zgtk-guri/Smart-Door-Keeper/3DPrint/STL/HandleVertical2.STL

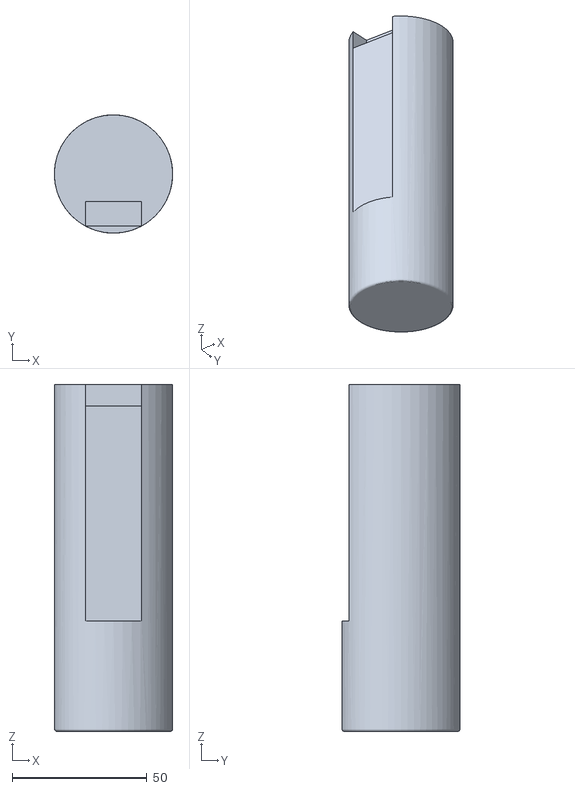
[picture p25: CAD file, 2018-07-12]
3DPrint/STL/HandleVertical2.STL
44.0 x 44.0 x 129.0
