zgtk-guri/Smart-Door-Keeper/3DPrint/STL/HandleVertical3.STL

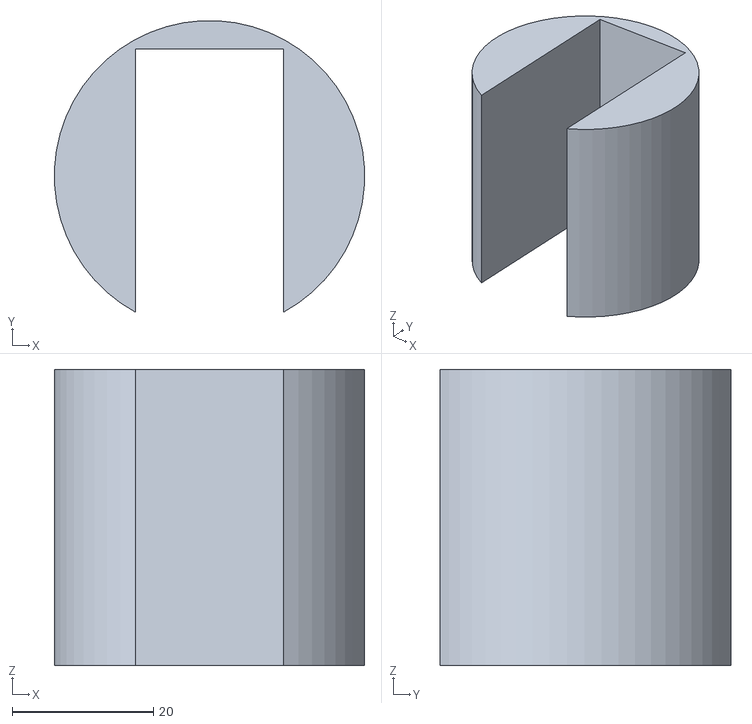
[picture p26: CAD file, 2018-07-12]
3DPrint/STL/HandleVertical3.STL
43.9 x 41.3 x 42.0
