zgtk-guri/Smart-Door-Keeper/3DPrint/Solidworks/KnobUpper.SLDPRT

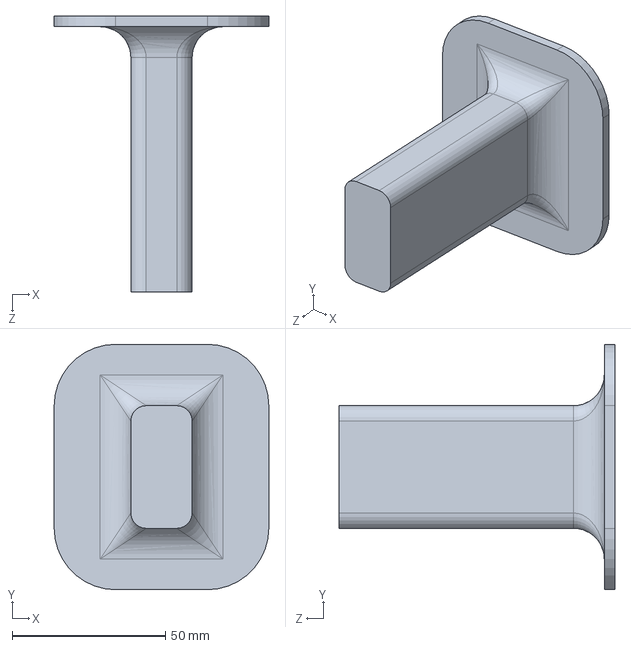
[picture p27: CAD file, 2018-07-12]
3DPrint/Solidworks/KnobUpper.SLDPRT
70.0 x 80.0 x 90.0 mm
