zgtk-guri/Smart-Door-Keeper/3DPrint/STL/SensorFoot1.STL

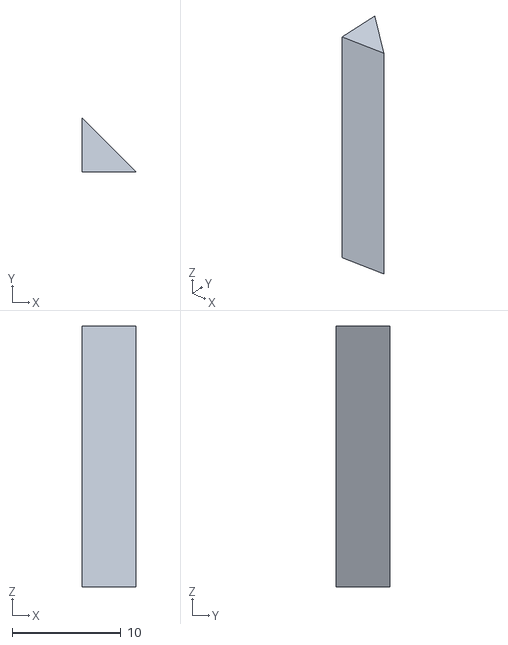
[picture p28: CAD file, 2018-07-12]
3DPrint/STL/SensorFoot1.STL
5.00 x 5.00 x 24.0
