zgtk-guri/Smart-Door-Keeper/3DPrint/Solidworks/ReedSwitch.SLDPRT

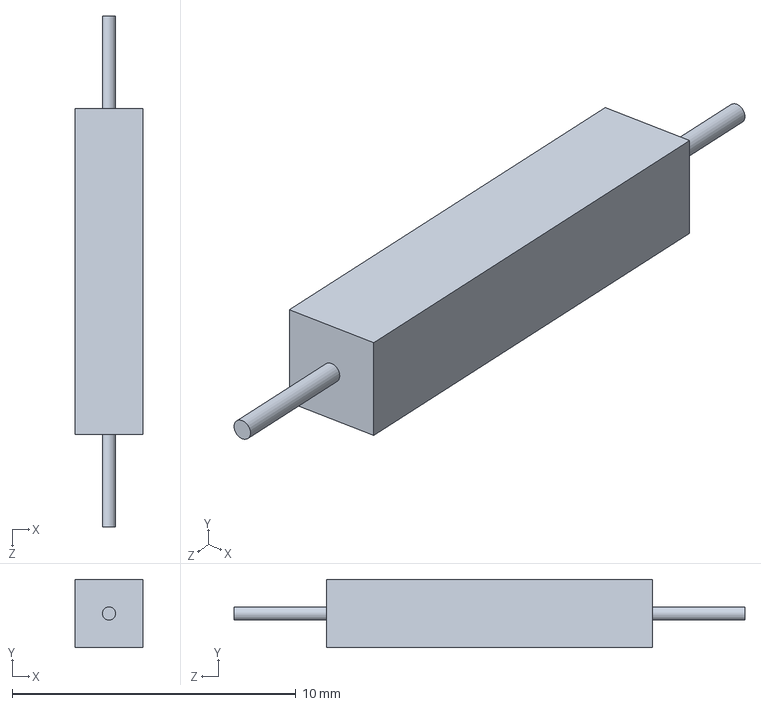
[picture p29: CAD file, 2018-07-12]
3DPrint/Solidworks/ReedSwitch.SLDPRT
2.40 x 2.40 x 18.0 mm
