zgtk-guri/Smart-Door-Keeper/3DPrint/Solidworks/PrintCircuitBoardSpacer.SLDPRT

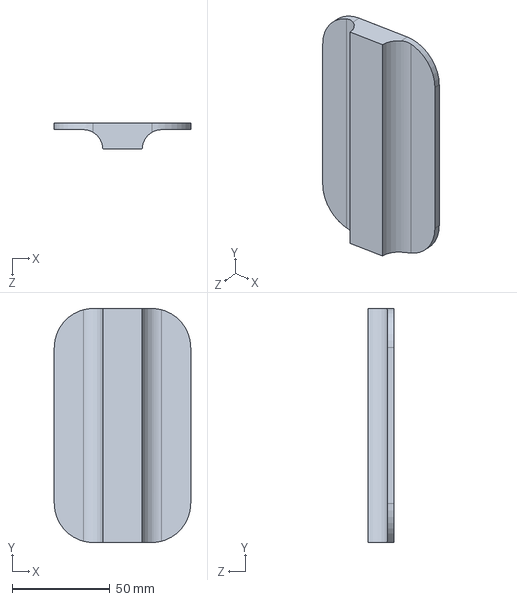
[picture p30: CAD file, 2018-07-12]
3DPrint/Solidworks/PrintCircuitBoardSpacer.SLDPRT
70.0 x 120.0 x 13.5 mm
