zgtk-guri/Smart-Door-Keeper/3DPrint/Solidworks/PrintCircuitBoardLid.SLDPRT

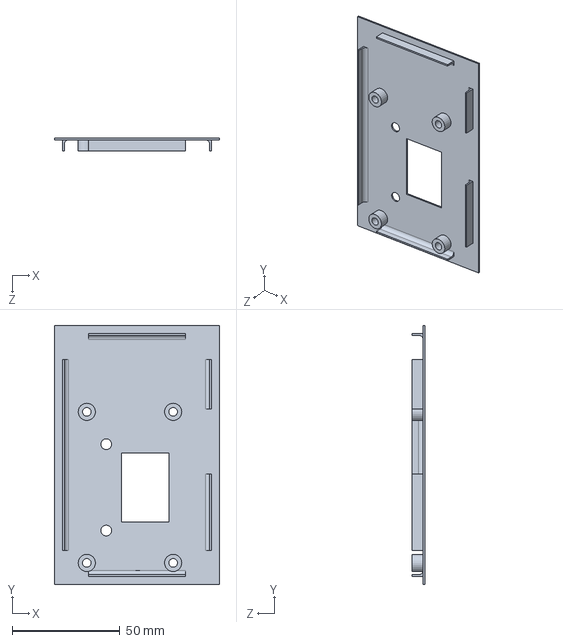
[picture p31: CAD file, 2018-07-12]
3DPrint/Solidworks/PrintCircuitBoardLid.SLDPRT
76.5 x 120.0 x 5.80 mm
