zgtk-guri/Smart-Door-Keeper/3DPrint/Solidworks/RotaterOfThumbTurnUpper.SLDPRT

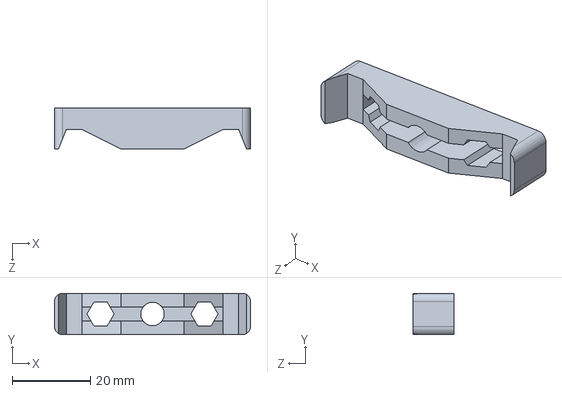
[picture p32: CAD file, 2018-07-12]
3DPrint/Solidworks/RotaterOfThumbTurnUpper.SLDPRT
50.0 x 10.5 x 10.5 mm
