zgtk-guri/Smart-Door-Keeper/3DPrint/Solidworks/LcdSpacer.SLDPRT

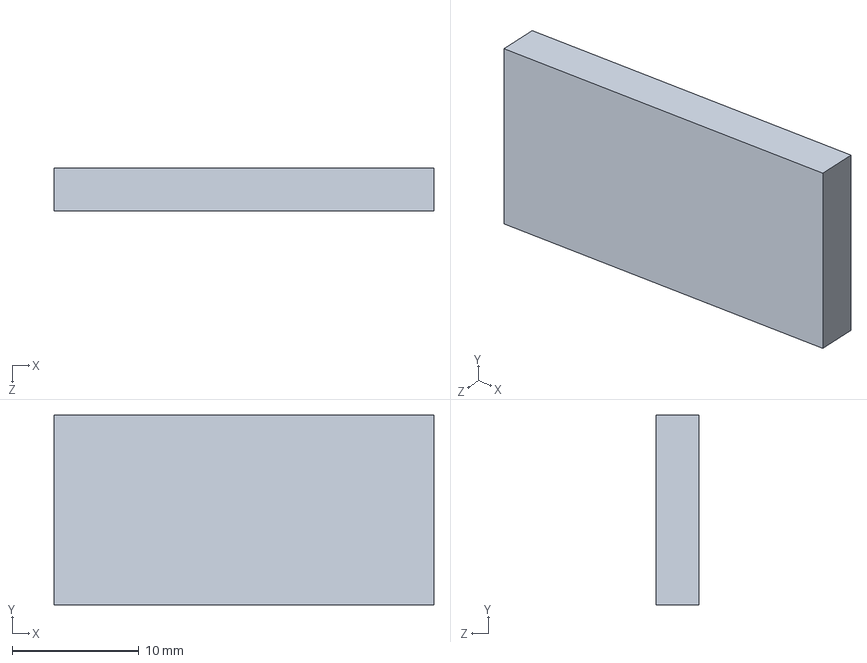
[picture p33: CAD file, 2018-07-12]
3DPrint/Solidworks/LcdSpacer.SLDPRT
30.0 x 15.0 x 3.40 mm
