zgtk-guri/Smart-Door-Keeper/3DPrint/Solidworks/PrintCircuitBoard.SLDPRT

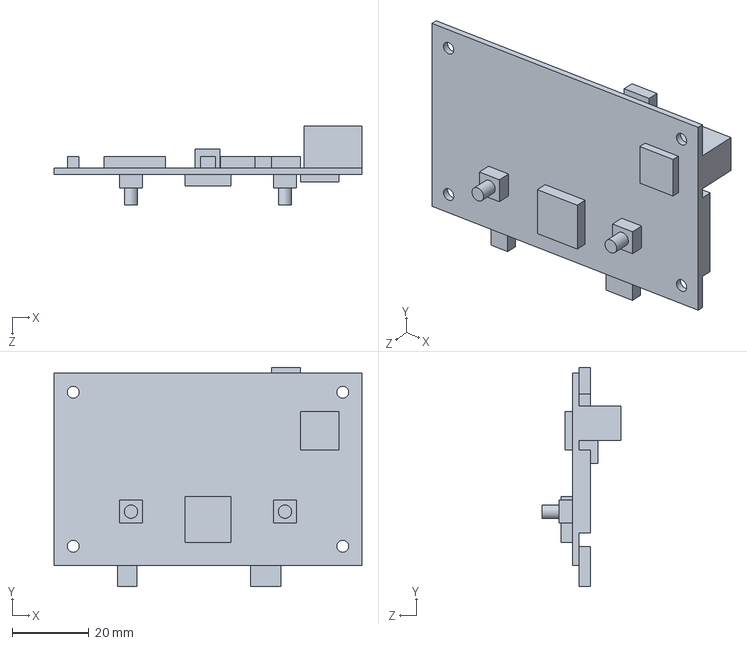
[picture p34: CAD file, 2018-07-12]
3DPrint/Solidworks/PrintCircuitBoard.SLDPRT
80.0 x 57.0 x 20.6 mm
