zgtk-guri/Smart-Door-Keeper/3DPrint/Solidworks/ServoArm.SLDPRT

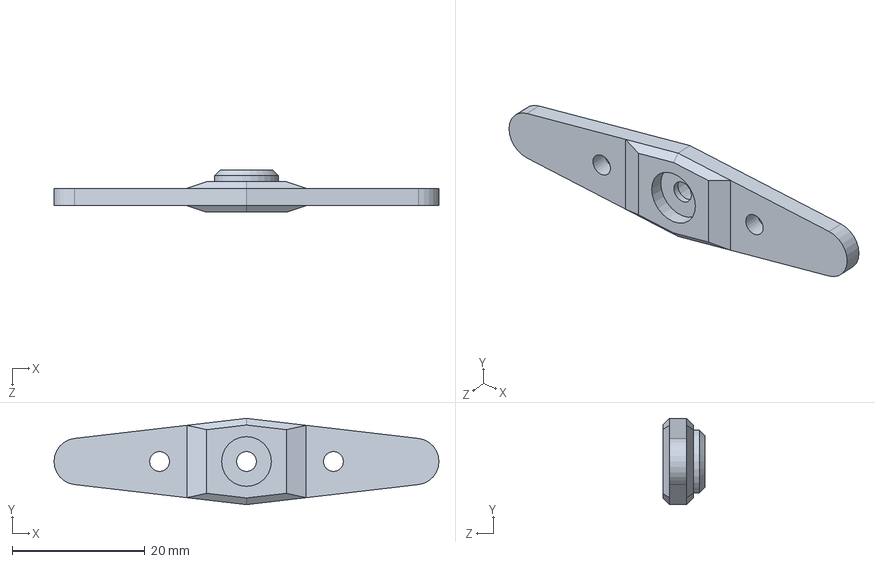
[picture p35: CAD file, 2018-07-12]
3DPrint/Solidworks/ServoArm.SLDPRT
58.0 x 13.0 x 6.40 mm
