zgtk-guri/Smart-Door-Keeper/3DPrint/Solidworks/Knob.SLDPRT

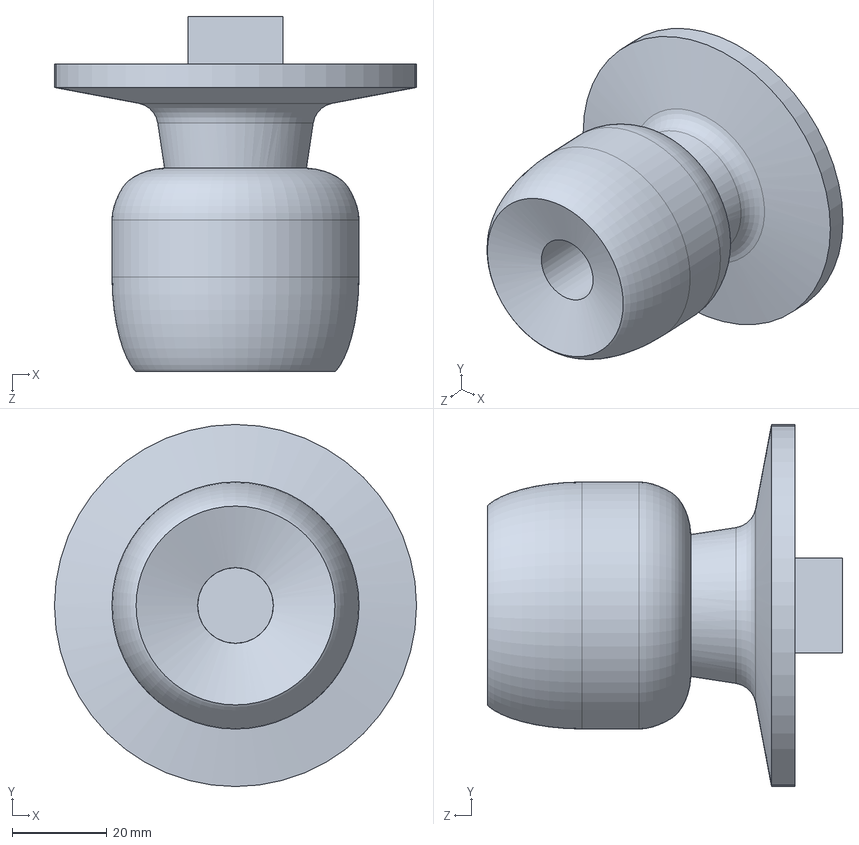
[picture p36: CAD file, 2018-07-12]
3DPrint/Solidworks/Knob.SLDPRT
76.5 x 76.5 x 75.0 mm
