zgtk-guri/Smart-Door-Keeper/3DPrint/Solidworks/NfcBox.SLDPRT

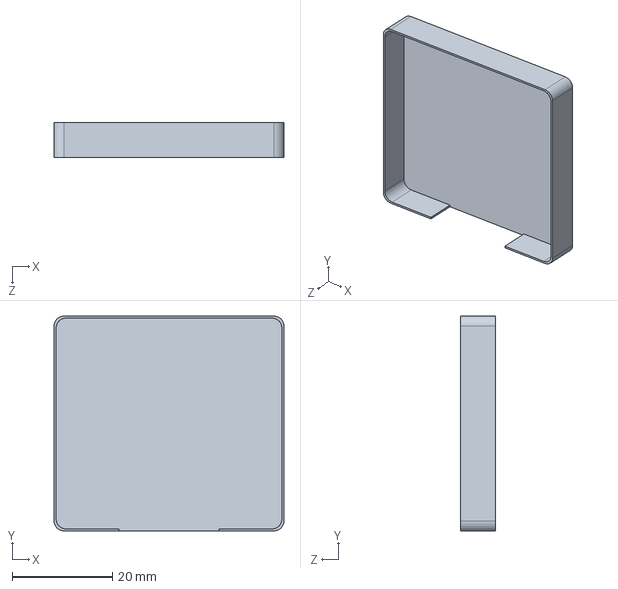
[picture p37: CAD file, 2018-07-12]
3DPrint/Solidworks/NfcBox.SLDPRT
45.8 x 42.8 x 7.00 mm
