zgtk-guri/Smart-Door-Keeper/3DPrint/Solidworks/ServoBody.SLDPRT

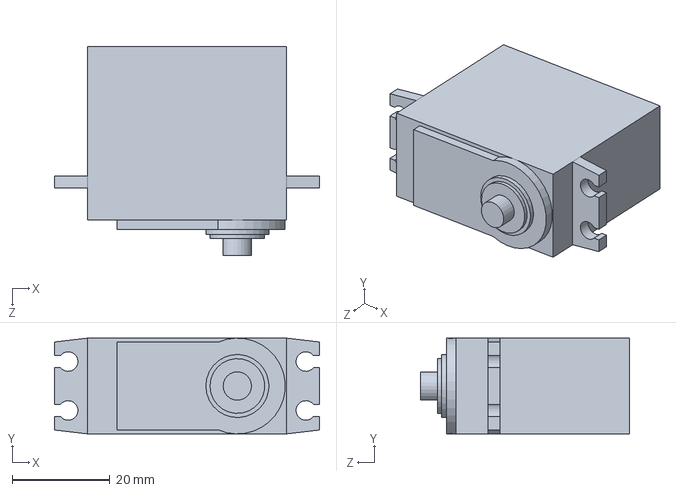
[picture p38: CAD file, 2018-07-12]
3DPrint/Solidworks/ServoBody.SLDPRT
54.2 x 19.6 x 42.8 mm
