zgtk-guri/Smart-Door-Keeper/3DPrint/Solidworks/HandleVertical.SLDPRT

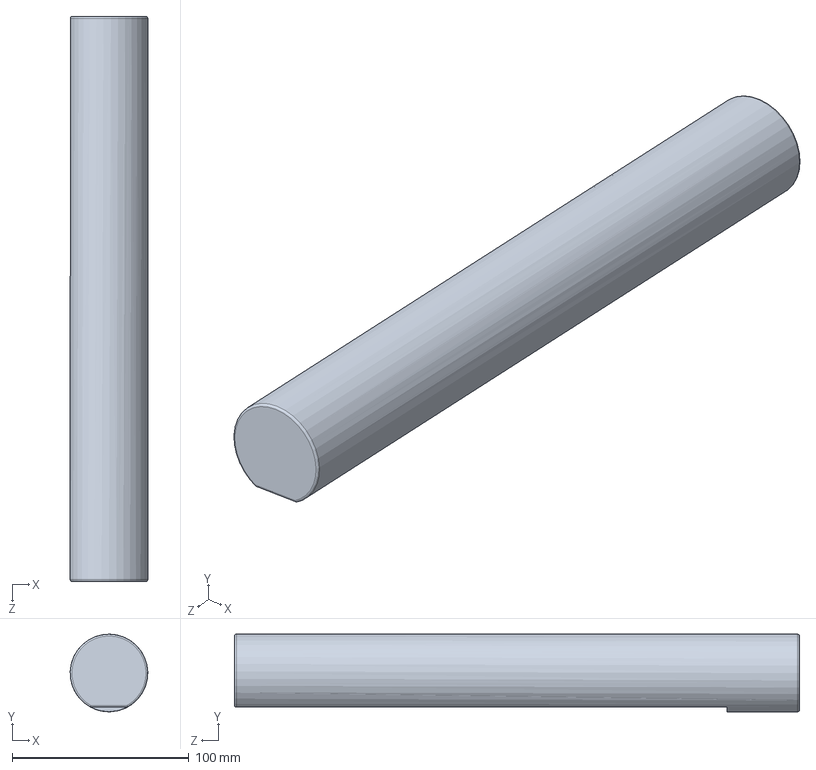
[picture p39: CAD file, 2018-07-12]
3DPrint/Solidworks/HandleVertical.SLDPRT
44.0 x 44.0 x 320.0 mm
