zgtk-guri/Smart-Door-Keeper/3DPrint/Solidworks/sumTurn.SLDPRT

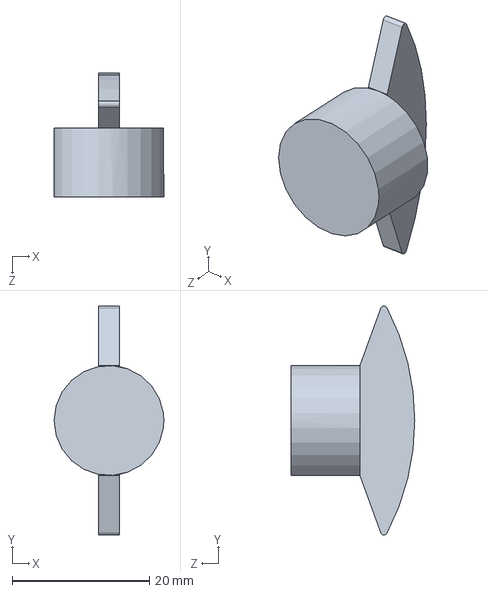
[picture p40: CAD file, 2018-07-12]
3DPrint/Solidworks/sumTurn.SLDPRT
16.0 x 33.4 x 18.0 mm
