zgtk-guri/Smart-Door-Keeper/3DPrint/Solidworks/NfcBoxLid.SLDPRT

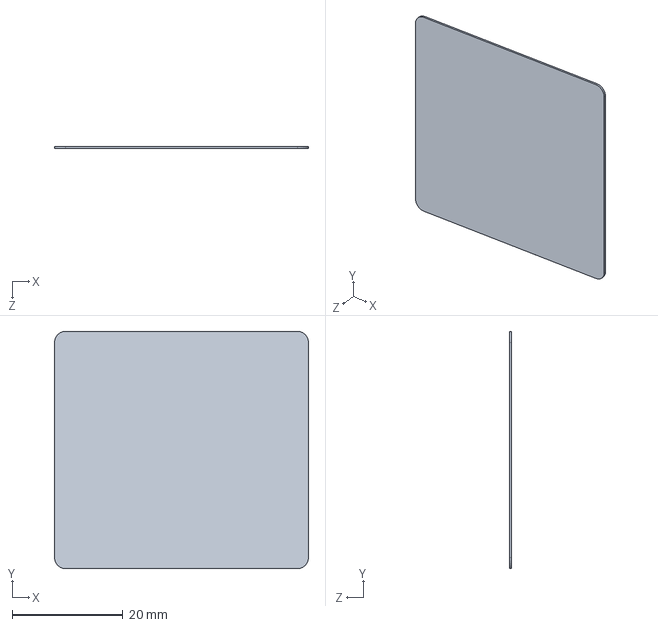
[picture p41: CAD file, 2018-07-12]
3DPrint/Solidworks/NfcBoxLid.SLDPRT
45.8 x 42.8 x 0.4 mm
