zgtk-guri/Smart-Door-Keeper/3DPrint/Solidworks/ReadSwitchLid.SLDPRT

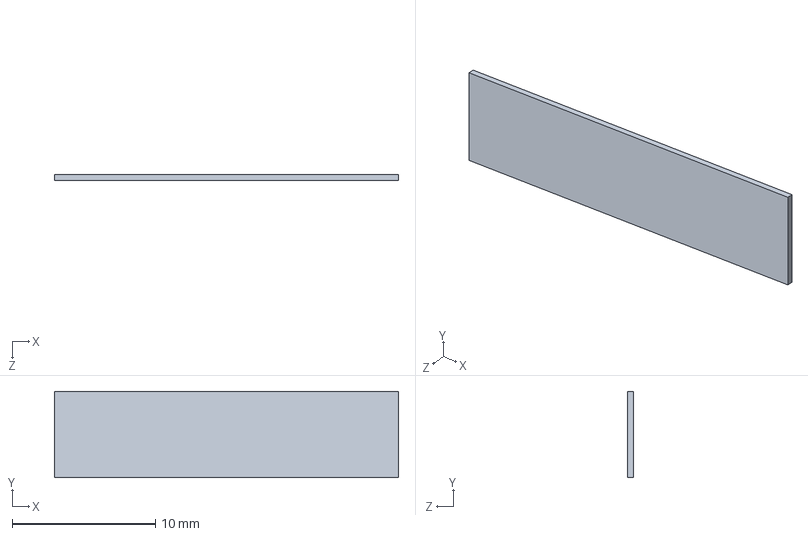
[picture p42: CAD file, 2018-07-12]
3DPrint/Solidworks/ReadSwitchLid.SLDPRT
24.0 x 6.00 x 0.4 mm
