zgtk-guri/Smart-Door-Keeper/3DPrint/Solidworks/RotaterOfThumbTurnLower.SLDPRT

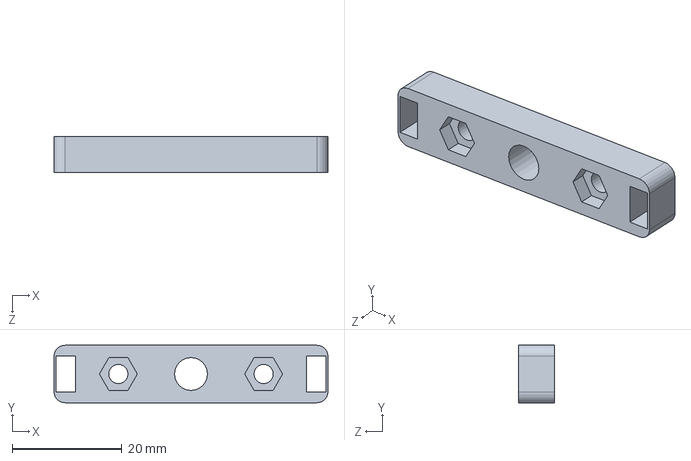
[picture p43: CAD file, 2018-07-12]
3DPrint/Solidworks/RotaterOfThumbTurnLower.SLDPRT
50.0 x 10.5 x 6.50 mm
